Cowlacious/k0wly-cw-keyer/images/20260712_120132.jpg

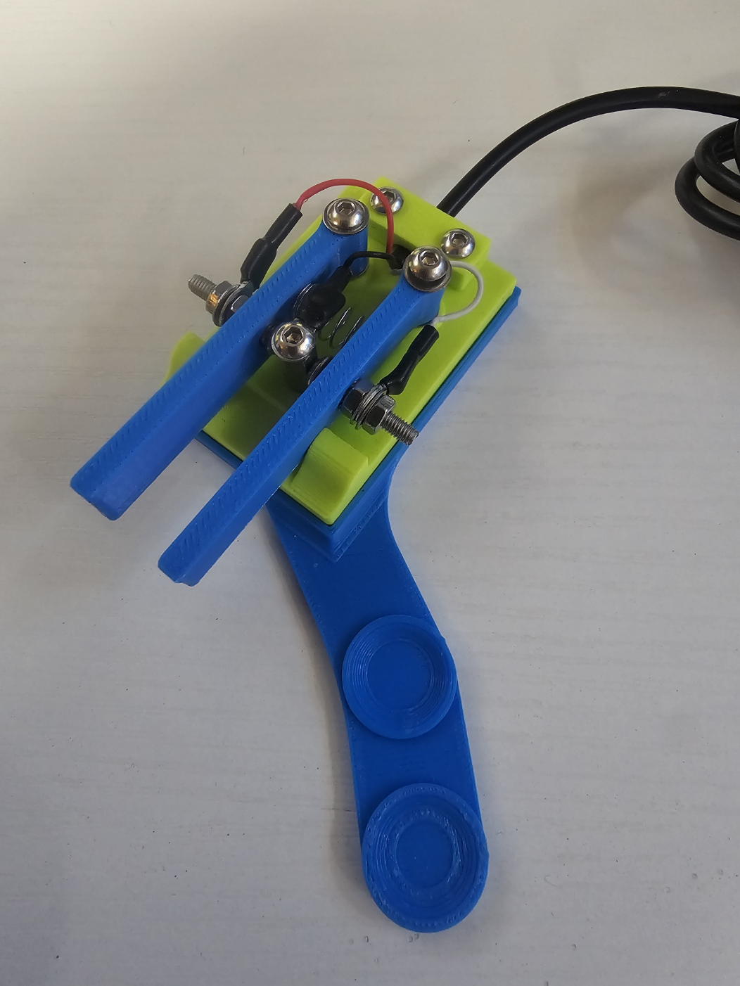
images/20260712_120132.jpg
