Cowlacious/k0wly-cw-keyer/images/20260808_221009.jpg

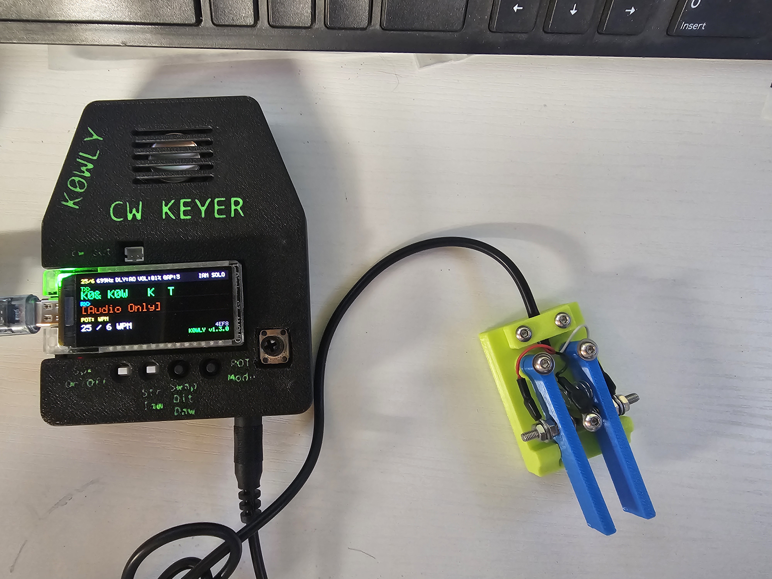
images/20260808_221009.jpg
