Cowlacious/k0wly-cw-keyer/images/20260920_120835.jpg

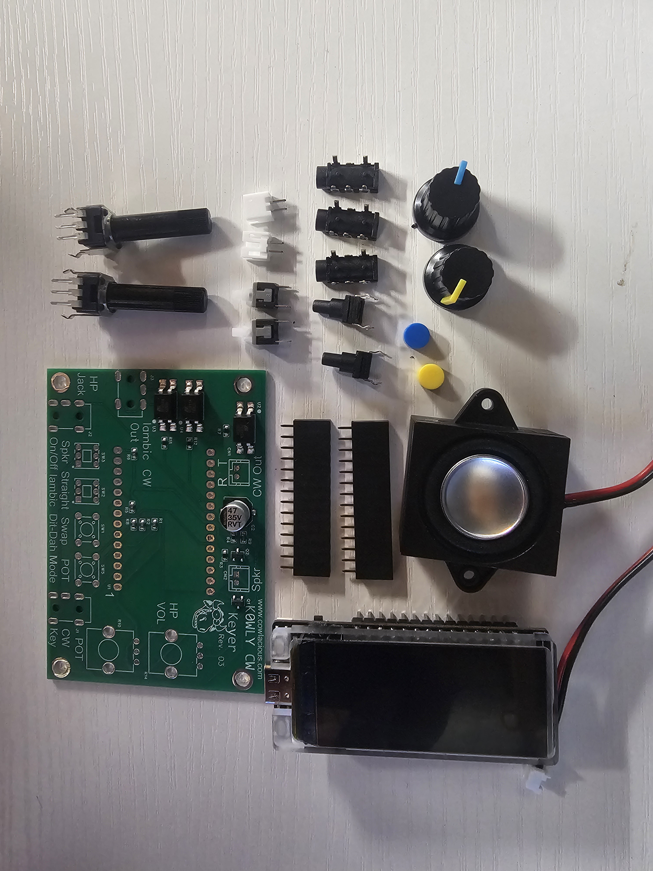
images/20260920_120835.jpg
